sheaivey/rx5808-pro-diversity/docs/img/rx5808-new-bottom.jpg

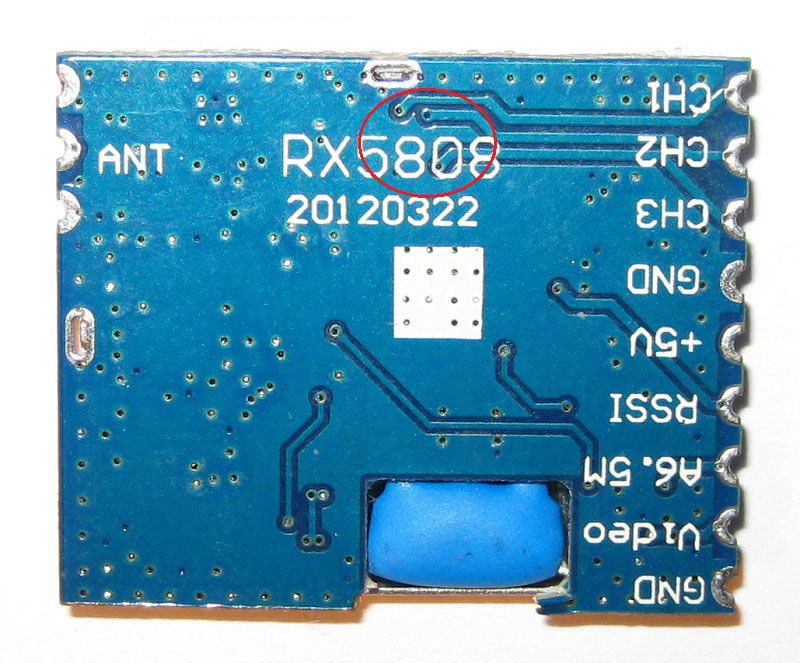
docs/img/rx5808-new-bottom.jpg
