sheaivey/rx5808-pro-diversity/docs/img/screens-tvout.jpg

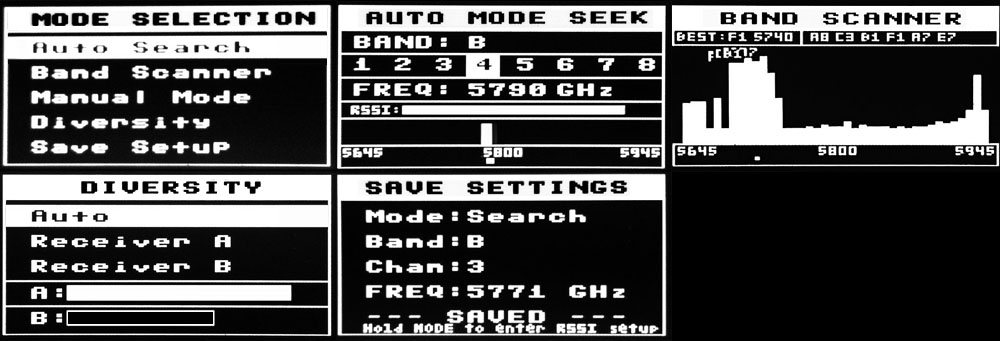
docs/img/screens-tvout.jpg
