sheaivey/rx5808-pro-diversity/src/rx5808-pro-diversity/state_screensaver.h

#ifndef STATE_SCREENSAVER_H
#define STATE_SCREENSAVER_H


#include "state.h"
#include "timer.h"
#include "settings.h"


namespace StateMachine {
    class ScreensaverStateHandler : public StateMachine::StateHandler {
        private:
            Timer displaySwapTimer = Timer(SCREENSAVER_DISPLAY_CYCLE * 1000);
            bool showLogo = false;

        public:
            void onEnter();
            void onUpdate();

            void onInitialDraw();
            void onUpdateDraw();

            void onButtonChange(Button button, Buttons::PressType pressType);
    };
}


#endif
