sheaivey/rx5808-pro-diversity/src/rx5808-pro-diversity/settings_eeprom.cpp

#include <string.h>
#include <EEPROM.h>

#include "settings.h"
#include "settings_internal.h"
#include "settings_eeprom.h"

#include "timer.h"


static Timer saveTimer = Timer(EEPROM_SAVE_TIME);
static bool isDirty = false;


struct EepromSettings EepromSettings;


void EepromSettings::update() {
    if (isDirty) {
        if (saveTimer.hasTicked()) {
            isDirty = false;
            saveTimer.reset();

            this->save();
        }
    }
}

void EepromSettings::load() {
    EEPROM.get(0, *this);

    if (this->magic != EEPROM_MAGIC)
        this->initDefaults();
}

void EepromSettings::save() {
    EEPROM.put(0, *this);
}

void EepromSettings::markDirty() {
    isDirty = true;
}


void EepromSettings::initDefaults() {
    memcpy_P(this, &EepromDefaults, sizeof(EepromDefaults));
    this->save();
}
