sheaivey/rx5808-pro-diversity/src/rx5808-pro-diversity/state_menu_ui.cpp

#include "state.h"
#include "state_menu.h"
#include "ui.h"
#include "ui_menu.h"
#include "pstr_helper.h"


#define TRIANGLE_SIZE 4
#define TRIANGLE_MARGIN 2

#define GRAPHIC_SIZE 32
#define GRAPHIC_X SCREEN_WIDTH_MID - (GRAPHIC_SIZE / 2)
#define GRAPHIC_Y 7

#define TEXT_Y SCREEN_HEIGHT - (CHAR_HEIGHT + 2) * 2

static void drawTriangles();
static void drawMenuEntry();


void StateMachine::MenuStateHandler::onInitialDraw() {
    Ui::clear();

    drawMenuEntry();
    drawTriangles();

    Ui::needDisplay();
}

void StateMachine::MenuStateHandler::onUpdateDraw() {
    Ui::clearRect(
        0,
        SCREEN_HEIGHT - (CHAR_HEIGHT + 2) * 2,
        SCREEN_WIDTH,
        (CHAR_HEIGHT + 2) * 2
    );

    drawMenuEntry();
    Ui::needDisplay();
}


void StateMachine::MenuStateHandler::drawMenuEntry() {
    const Ui::MenuItem* item = this->menu.getCurrentItem();
    const uint8_t charLen = strlen(PSTRtoBuffer_P(item->text));

    Ui::display.setTextSize(2);
    Ui::display.setTextColor(WHITE);
    Ui::display.setCursor(
        SCREEN_WIDTH_MID - (charLen * ((CHAR_WIDTH + 1) * 2)) / 2,
        TEXT_Y
    );
    Ui::display.print(PSTRtoBuffer_P(item->text));

    if (item->icon) {
        Ui::clearRect(
            GRAPHIC_X,
            GRAPHIC_Y,
            GRAPHIC_SIZE,
            GRAPHIC_SIZE
        );

        Ui::display.drawBitmap(
            GRAPHIC_X,
            GRAPHIC_Y,
            item->icon,
            GRAPHIC_SIZE,
            GRAPHIC_SIZE,
            WHITE
        );
    }
}

static void drawTriangles() {
    Ui::display.fillTriangle(
        SCREEN_WIDTH - 1 - (TRIANGLE_SIZE),
        SCREEN_HEIGHT_MID + TRIANGLE_MARGIN,

        SCREEN_WIDTH - 1 - (TRIANGLE_SIZE / 2),
        SCREEN_HEIGHT_MID + TRIANGLE_MARGIN + (TRIANGLE_SIZE),

        SCREEN_WIDTH - 1,
        SCREEN_HEIGHT_MID + TRIANGLE_MARGIN,

        WHITE
    );

    Ui::display.fillTriangle(
        SCREEN_WIDTH - 1 - (TRIANGLE_SIZE),
        SCREEN_HEIGHT_MID - TRIANGLE_MARGIN,

        SCREEN_WIDTH - 1 - (TRIANGLE_SIZE / 2),
        SCREEN_HEIGHT_MID - TRIANGLE_MARGIN - (TRIANGLE_SIZE),

        SCREEN_WIDTH - 1,
        SCREEN_HEIGHT_MID - TRIANGLE_MARGIN,

        WHITE
    );
}
